bradkim06/gas_nordic/hardware/gas_nrf52832/pcb/2차_Rev1.0.2(4L)/24.9.19 검수조서/9.19 검수조서 사진/1.jpg

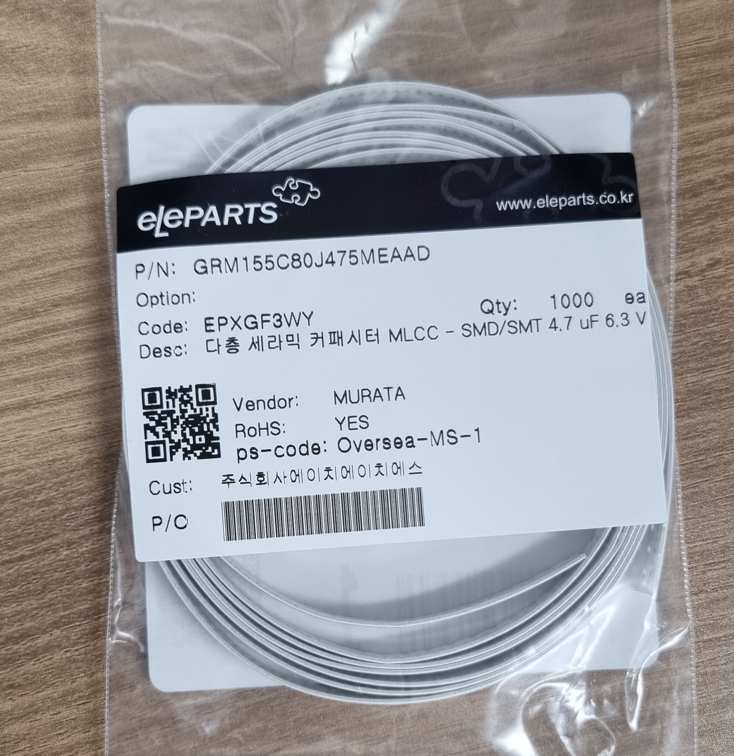
hardware/gas_nrf52832/pcb/2차_Rev1.0.2(4L)/24.9.19 검수조서/9.19 검수조서 사진/1.jpg
