bradkim06/gas_nordic/hardware/gas_nrf52832/pcb/2차_Rev1.0.2(4L)/24.9.26 검수조서/9.26 검수조서 사진/KakaoTalk_20240926_162621671.jpg

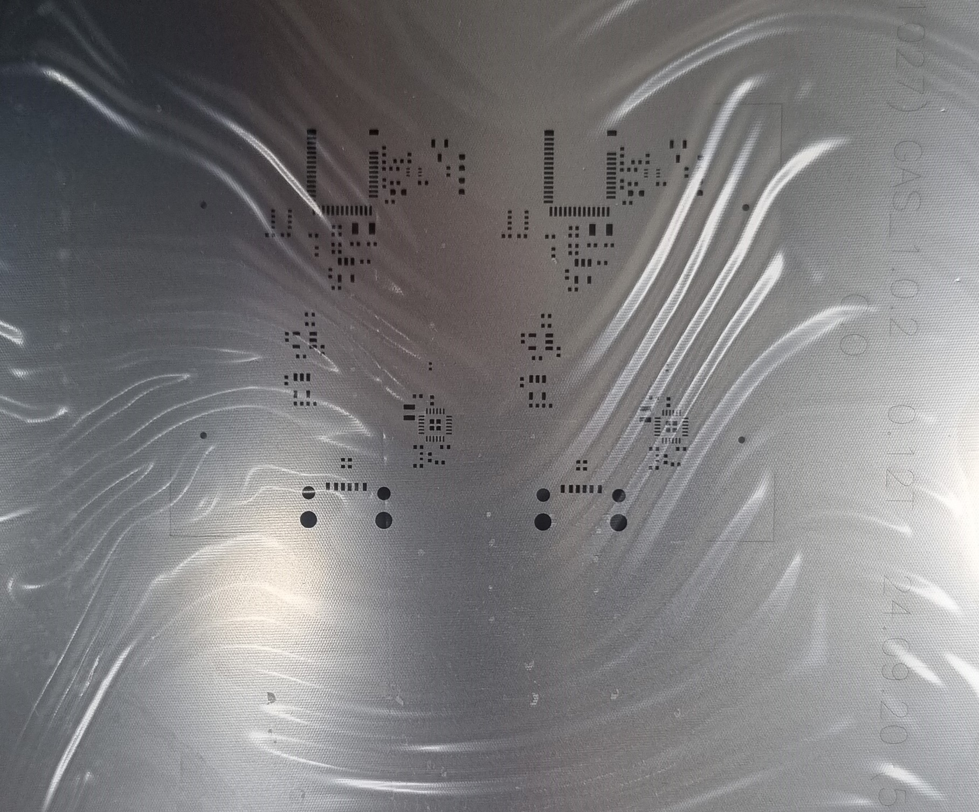
hardware/gas_nrf52832/pcb/2차_Rev1.0.2(4L)/24.9.26 검수조서/9.26 검수조서 사진/KakaoTalk_20240926_162621671.jpg
