bradkim06/gas_nordic/hardware/gas_nrf52832/pcb/3차_Rev1.0.3/문서/24.10.15 검수조서/10.15 검수조서 사진/KakaoTalk_20241015_093432720.jpg

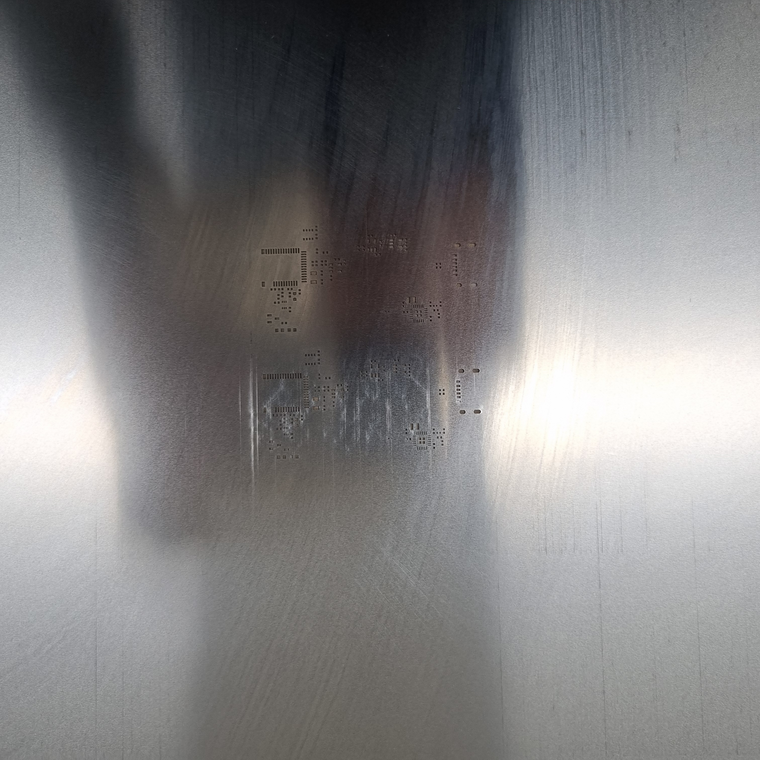
hardware/gas_nrf52832/pcb/3차_Rev1.0.3/문서/24.10.15 검수조서/10.15 검수조서 사진/KakaoTalk_20241015_093432720.jpg
