bradkim06/gas_nordic/doc/gas_nrf52832_rev1.0.1.pdf

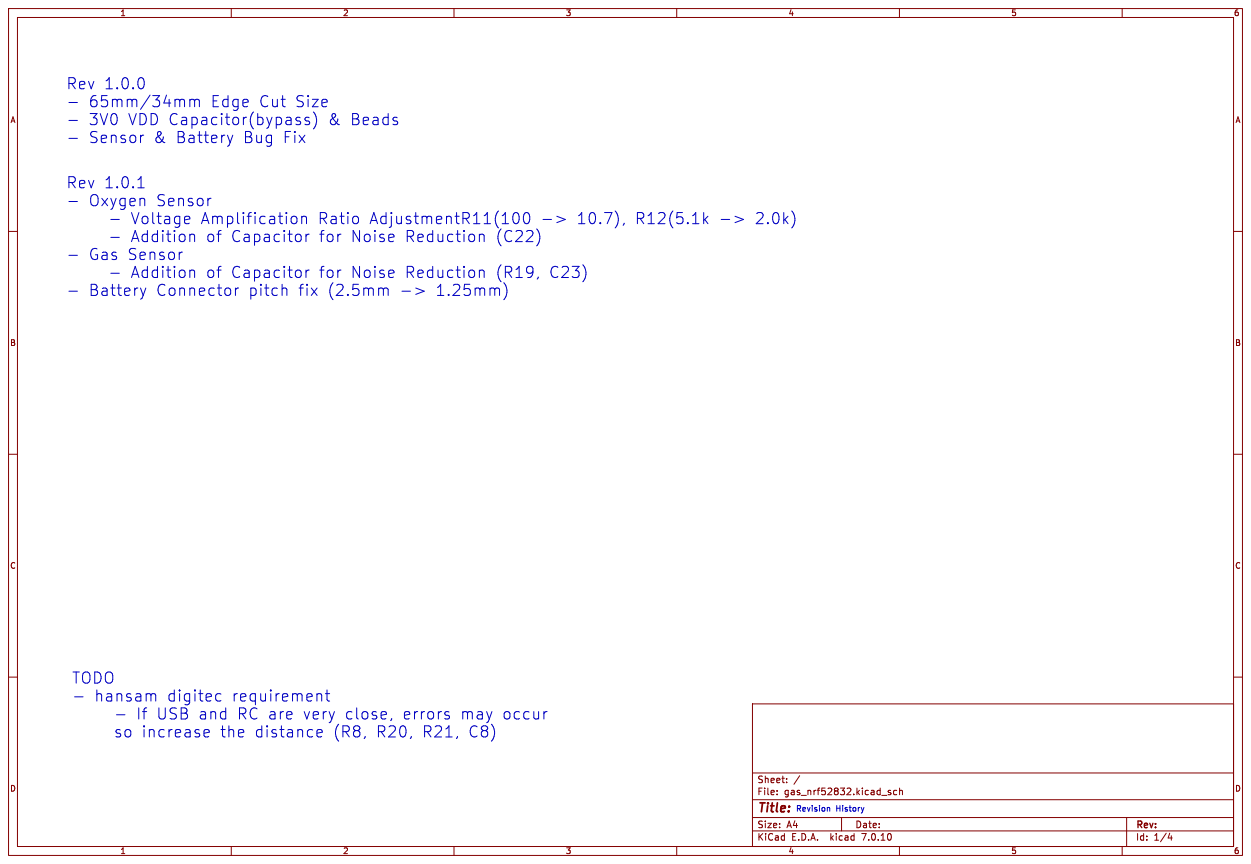
[picture p50: page 1]

Id: 1/4 Title: File: gas_nrf52832.kicad_sch Sheet: / nrf52832

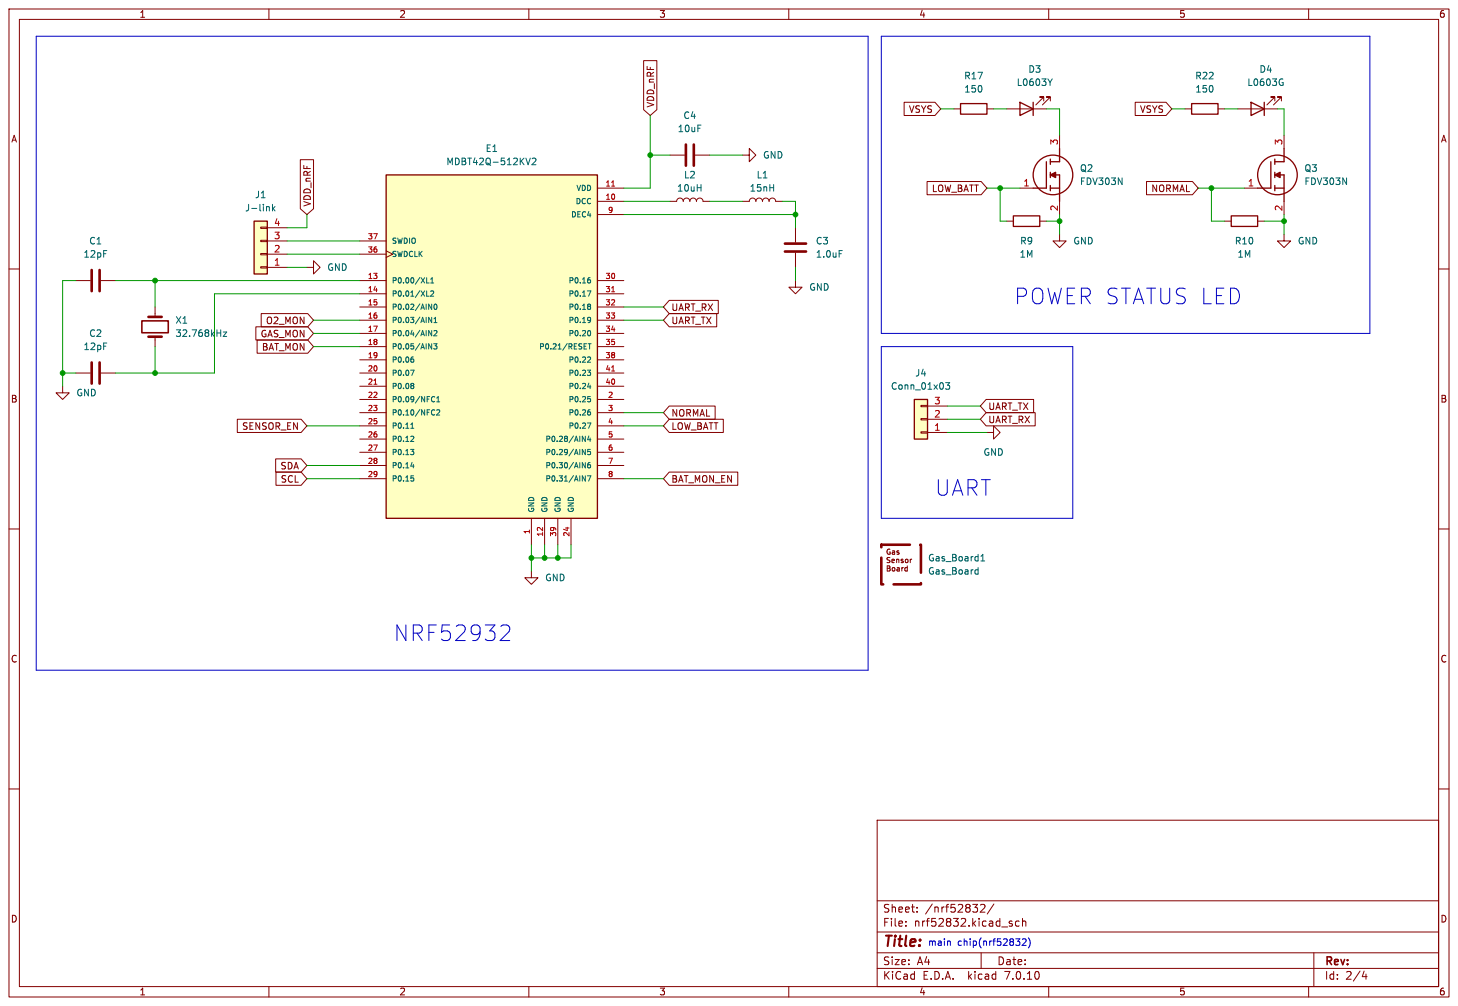
[picture p51: page 2]

1 DCC 10 VDD 11 GND 12 P0.00/XL1 13 P0.01/XL2 14 P0.06 19 P0.25 2 P0.07 20 P0.08 21 GND 24 P0.11 25 P0.12 26 P0.13 27 P0.14 28 P0.15 29 P0.26 3 P0.16 30 P0.17 31 P0.18 32 P0.19 33 P0.20 34 P0.21/RESET 35 SWDCLK 36 SWDIO 37 P0.22 38 GND 39 P0.27 4 P0.24 40 P0.23 41 DEC4 9 P0.02/AIN0 15 P0.03/AIN1 16 P0.04/AIN2 17 P0.05/AIN3 18 P0.09/NFC1 22 P0.10/NFC2 23 P0.28/AIN4 5 P0.29/AIN5 6 P0.30/AIN6 7 P0.31/AIN7 8 E1 MDBT42Q-512KV2 C4

Id: 2/4 Title: File: nrf52832.kicad_sch Sheet: /nrf52832/

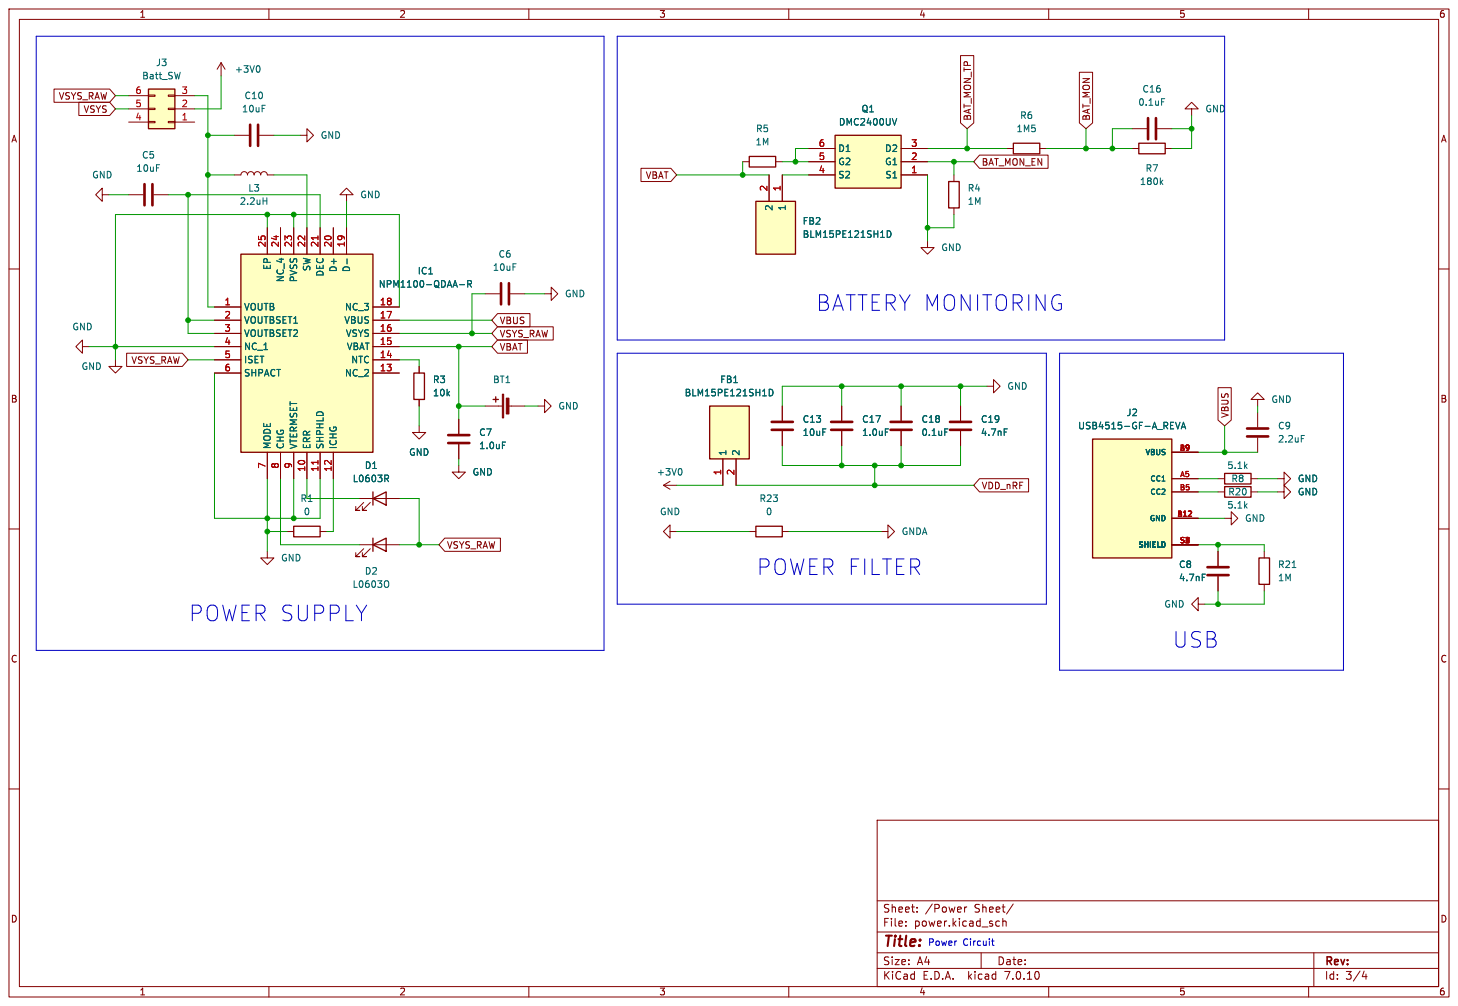
[picture p52: page 3]

2.2uF GND GND GND GND

Power Circuit POWER FILTER

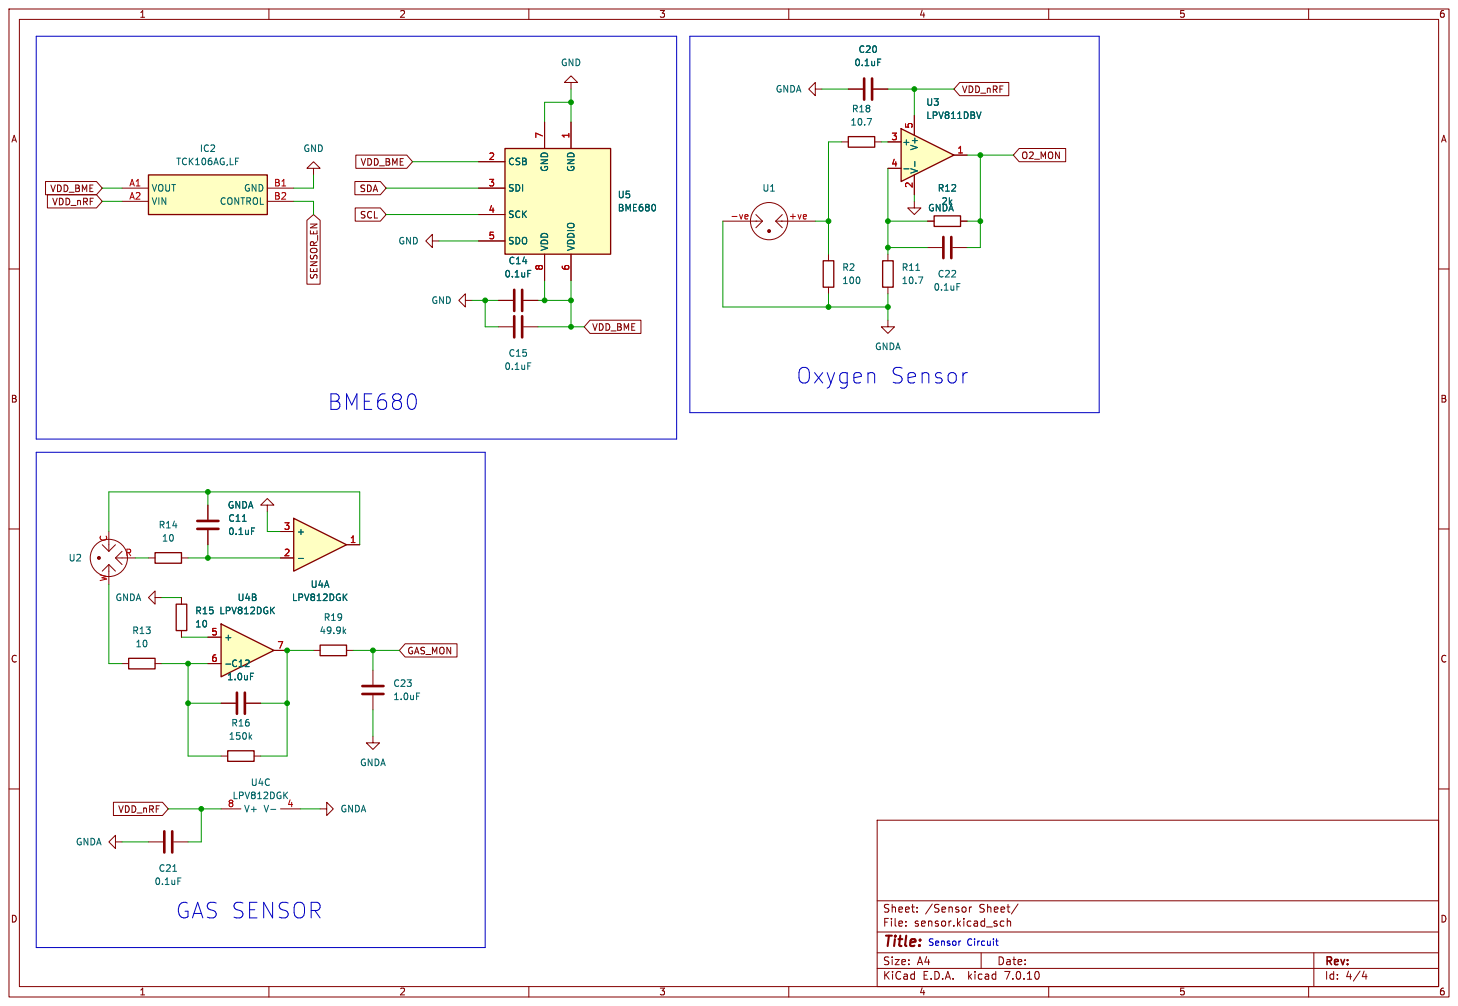
[picture p53: page 4]

1 CSB 2 SDI 3 SCK 4 SDO 5 VDDIO
