bradkim06/gas_nordic/hardware/gas_nrf52832/pcb/3차_Rev1.0.3/gas_layout_1.0.3.pdf

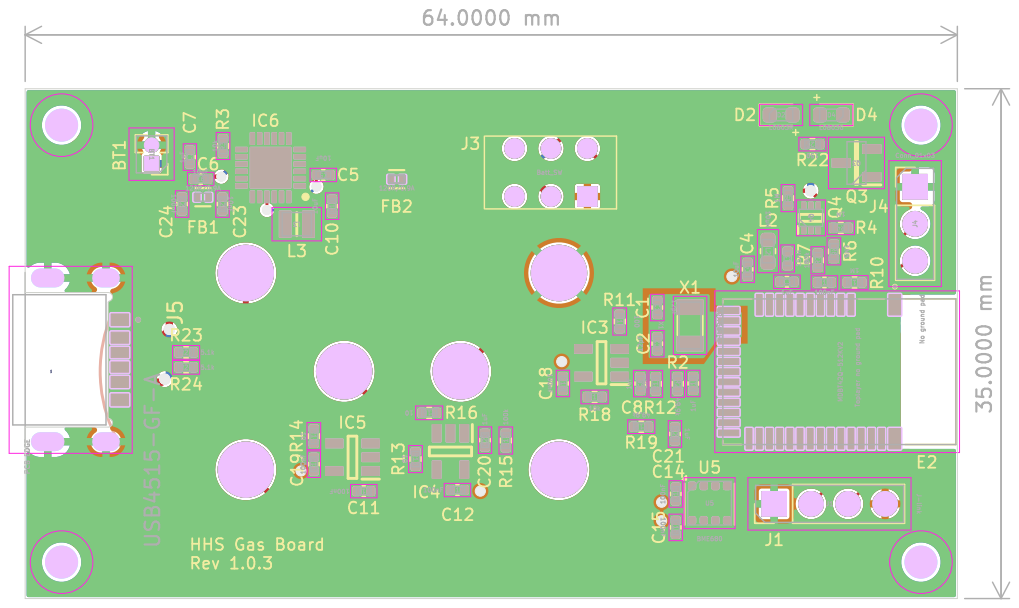
[picture p63: page 1]
